sekigon-gonnoc/meEC/img/img1.JPG

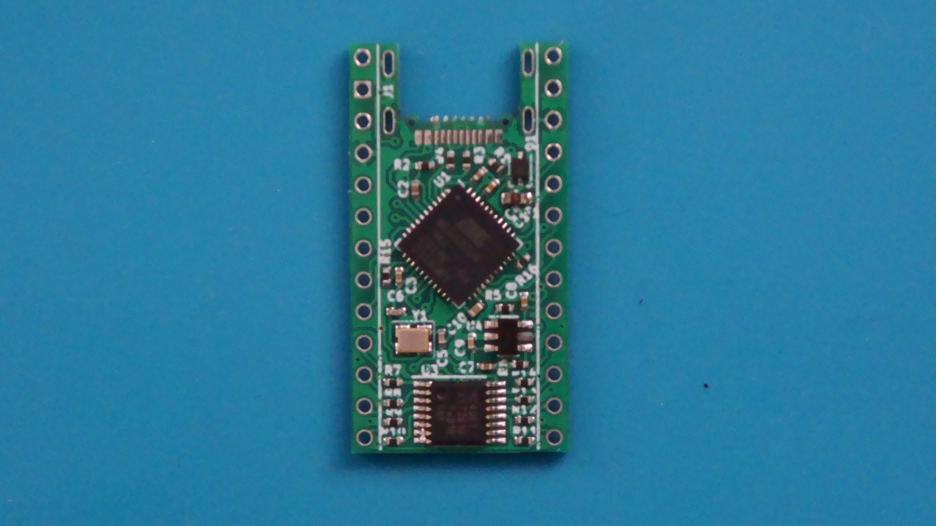
img/img1.JPG
