sekigon-gonnoc/meEC/img/img3.JPG

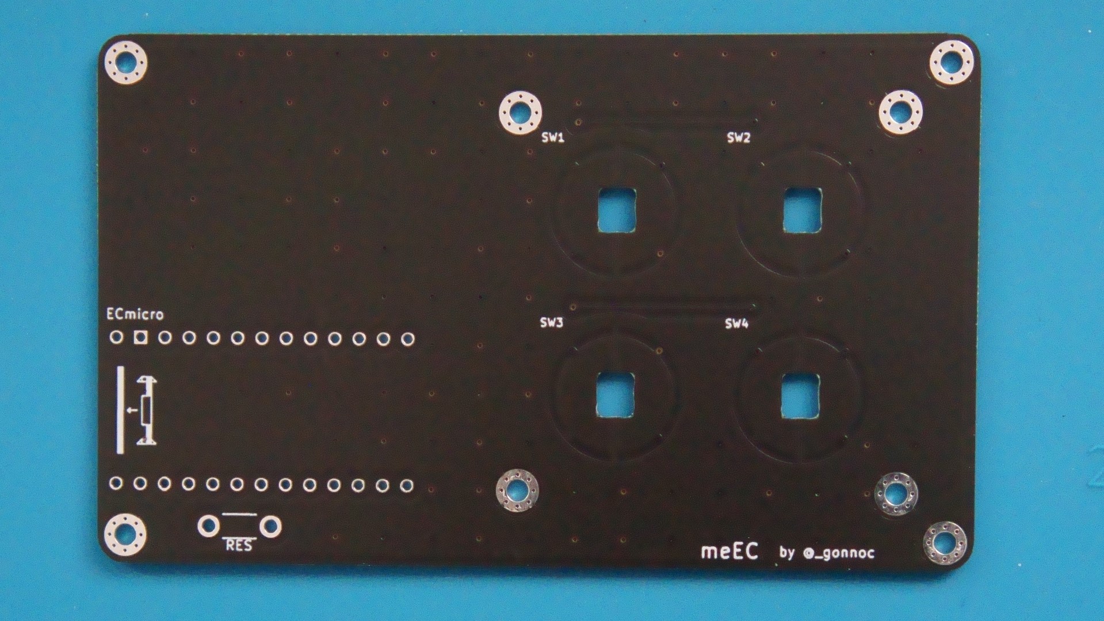
img/img3.JPG
