sekigon-gonnoc/meEC/img/img4.JPG

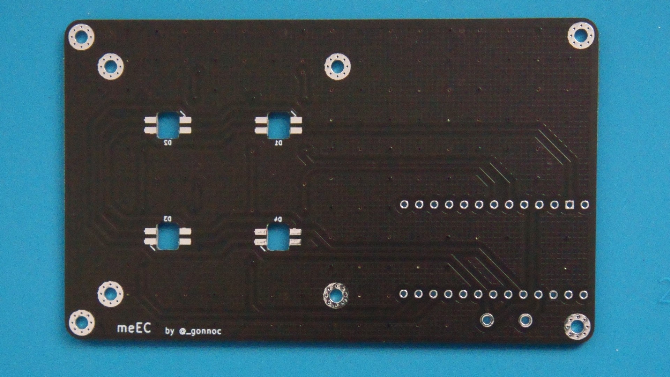
img/img4.JPG
