sekigon-gonnoc/meEC/img/img8.JPG

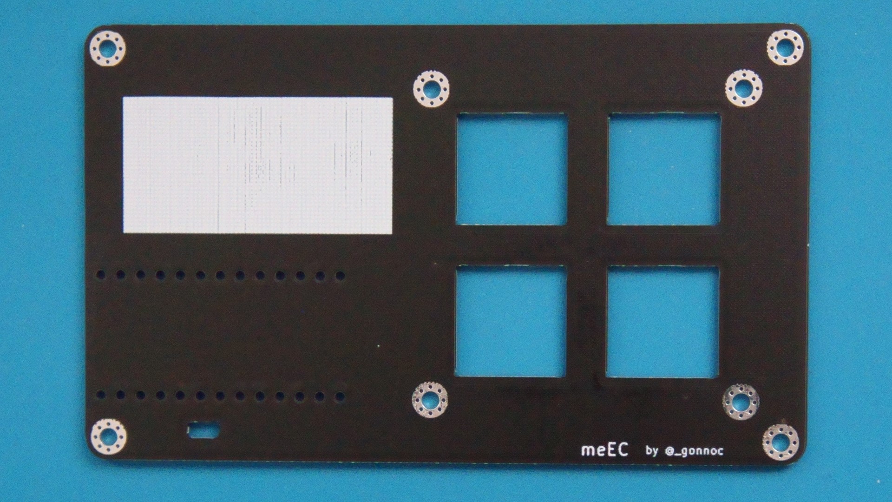
img/img8.JPG
